xqe2011/saihub/hardware/mechanical/output/preview.png

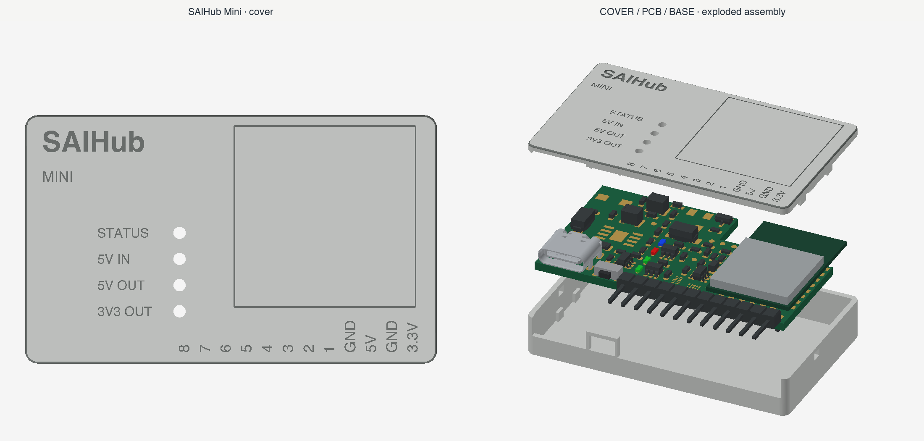
hardware/mechanical/output/preview.png
