xqe2011/saihub/main/src/uart_ctrl.c

/**
 * @name UART control module
 * @file uart_ctrl.c
 * @author xqe2011
 */
#include "uart_ctrl.h"

#include "config.h"
#include "gpio_ctrl.h"
#include "lock.h"
#include "tool.h"

#include <driver/uart.h>
#include <esp_log.h>
#include <freertos/FreeRTOS.h>
#include <freertos/semphr.h>
#include <stdio.h>
#include <string.h>

static const char* tag = "SAIHub-Uart";

static const int uartIdToNum[] = CONFIG_UART_ID_TO_NUM;

typedef struct {
  UartCtrl_Config cfg;
  bool driverInstalled;
  char owner[32];
} UartCtrl_Runtime;

static UartCtrl_Runtime uarts[TOOL_GET_ARRAY_LENGTH(uartIdToNum)];
static SemaphoreHandle_t mutex;

bool UartCtrl_IsValidId(int id)
{
  return id >= 0 && id < (int)TOOL_GET_ARRAY_LENGTH(uartIdToNum);
}

int UartCtrl_GetCount(void)
{
  return (int)TOOL_GET_ARRAY_LENGTH(uartIdToNum);
}

const char* UartCtrl_ParityToString(UartCtrl_Parity p)
{
  switch (p) {
    case UART_CTRL_PARITY_EVEN:
      return "even";
    case UART_CTRL_PARITY_ODD:
      return "odd";
    case UART_CTRL_PARITY_NONE:
    default:
      return "none";
  }
}

bool UartCtrl_ParityFromString(const char* s, UartCtrl_Parity* out)
{
  if (s == NULL || out == NULL) return false;
  if (strcmp(s, "none") == 0) {
    *out = UART_CTRL_PARITY_NONE;
    return true;
  }
  if (strcmp(s, "even") == 0) {
    *out = UART_CTRL_PARITY_EVEN;
    return true;
  }
  if (strcmp(s, "odd") == 0) {
    *out = UART_CTRL_PARITY_ODD;
    return true;
  }
  return false;
}

const char* UartCtrl_EncodingToString(UartCtrl_Encoding e)
{
  return e == UART_CTRL_ENCODING_BYTE ? "byte" : "utf8";
}

bool UartCtrl_EncodingFromString(const char* s, UartCtrl_Encoding* out)
{
  if (s == NULL || out == NULL) return false;
  if (strcmp(s, "utf8") == 0) {
    *out = UART_CTRL_ENCODING_UTF8;
    return true;
  }
  if (strcmp(s, "byte") == 0) {
    *out = UART_CTRL_ENCODING_BYTE;
    return true;
  }
  return false;
}

static uart_port_t UartCtrl_HwPort(int id)
{
  return (uart_port_t)uartIdToNum[id];
}

static uart_word_length_t UartCtrl_ToWordLength(int dataBits)
{
  switch (dataBits) {
    case 5:
      return UART_DATA_5_BITS;
    case 6:
      return UART_DATA_6_BITS;
    case 7:
      return UART_DATA_7_BITS;
    case 8:
    default:
      return UART_DATA_8_BITS;
  }
}

static uart_parity_t UartCtrl_ToParity(UartCtrl_Parity p)
{
  switch (p) {
    case UART_CTRL_PARITY_EVEN:
      return UART_PARITY_EVEN;
    case UART_CTRL_PARITY_ODD:
      return UART_PARITY_ODD;
    case UART_CTRL_PARITY_NONE:
    default:
      return UART_PARITY_DISABLE;
  }
}

static uart_stop_bits_t UartCtrl_ToStopBits(int stopBits)
{
  return stopBits == 2 ? UART_STOP_BITS_2 : UART_STOP_BITS_1;
}

static void UartCtrl_MakeOwner(int id, char* out, size_t outLen)
{
  snprintf(out, outLen, "uart:%d", id);
}

static esp_err_t UartCtrl_ValidateConfig(const UartCtrl_Config* cfg, char* reason, size_t reasonLen)
{
  if (cfg == NULL) return ESP_ERR_INVALID_ARG;
  if (cfg->baudRate < 1) {
    snprintf(reason, reasonLen, "baudRate must be a positive integer.");
    return ESP_ERR_INVALID_ARG;
  }
  if (cfg->dataBits < 5 || cfg->dataBits > 8) {
    snprintf(reason, reasonLen, "dataBits must be 5, 6, 7, or 8.");
    return ESP_ERR_INVALID_ARG;
  }
  if (cfg->stopBits != 1 && cfg->stopBits != 2) {
    snprintf(reason, reasonLen, "stopBits must be 1 or 2.");
    return ESP_ERR_INVALID_ARG;
  }
  if (cfg->rxPin >= 0 && !GpioCtrl_IsValidLogicalPin(cfg->rxPin)) {
    snprintf(reason, reasonLen, "pins.rx is invalid. Use a pin from 0 to %d or omit it.",
             GpioCtrl_GetLogicalCount() - 1);
    return ESP_ERR_INVALID_ARG;
  }
  if (cfg->txPin >= 0 && !GpioCtrl_IsValidLogicalPin(cfg->txPin)) {
    snprintf(reason, reasonLen, "pins.tx is invalid. Use a pin from 0 to %d or omit it.",
             GpioCtrl_GetLogicalCount() - 1);
    return ESP_ERR_INVALID_ARG;
  }
  if (cfg->rxPin >= 0 && cfg->txPin >= 0 && cfg->rxPin == cfg->txPin) {
    snprintf(reason, reasonLen, "pins.rx and pins.tx must be different when both are set.");
    return ESP_ERR_INVALID_ARG;
  }
  if (cfg->enable && cfg->rxPin < 0 && cfg->txPin < 0) {
    snprintf(reason, reasonLen, "enable true requires at least one of pins.rx or pins.tx.");
    return ESP_ERR_INVALID_ARG;
  }
  return ESP_OK;
}

static void UartCtrl_BuildPinResources(const UartCtrl_Config* cfg, Lock_Resource* out, size_t* countOut)
{
  size_t n = 0;
  if (cfg->rxPin >= 0) {
    out[n].kind = LOCK_KIND_GPIO;
    out[n].pin = cfg->rxPin;
    out[n].methods = LOCK_METHOD_READ | LOCK_METHOD_WRITE;
    n++;
  }
  if (cfg->txPin >= 0) {
    out[n].kind = LOCK_KIND_GPIO;
    out[n].pin = cfg->txPin;
    out[n].methods = LOCK_METHOD_READ | LOCK_METHOD_WRITE;
    n++;
  }
  *countOut = n;
}

static void UartCtrl_DisablePinModes(const UartCtrl_Config* cfg)
{
  if (cfg->rxPin >= 0) {
    GpioCtrl_SetConfig(cfg->rxPin, GPIO_CTRL_MODE_DISABLE, false, false, false);
  }
  if (cfg->txPin >= 0) {
    GpioCtrl_SetConfig(cfg->txPin, GPIO_CTRL_MODE_DISABLE, false, false, false);
  }
}

static esp_err_t UartCtrl_StartDriver(int id, const UartCtrl_Config* cfg, char* reason, size_t reasonLen)
{
  Lock_Resource resources[2];
  size_t resourceCount = 0;
  UartCtrl_BuildPinResources(cfg, resources, &resourceCount);

  char owner[32];
  UartCtrl_MakeOwner(id, owner, sizeof(owner));
  Lock_Conflict conflict;
  memset(&conflict, 0, sizeof(conflict));
  esp_err_t aret = Lock_AcquirePeripheral(owner, resources, resourceCount, &conflict);
  if (aret == ESP_ERR_INVALID_STATE) {
    if (conflict.isPeripheral) {
      const char* label = conflict.peripheralLabel[0] ? conflict.peripheralLabel : "a peripheral";
      snprintf(reason, reasonLen, "Pin %d is reserved by %s. Disable %s or use other pins.", conflict.pin, label,
               label);
    } else {
      snprintf(reason, reasonLen,
               "Pin %d is already held by a lock. DELETE that lock or wait until it expires before enabling UART.",
               conflict.pin);
    }
    return ESP_ERR_INVALID_STATE;
  }
  if (aret != ESP_OK) {
    snprintf(reason, reasonLen, "internal");
    return aret;
  }

  UartCtrl_DisablePinModes(cfg);

  uart_config_t ucfg = {
      .baud_rate = cfg->baudRate,
      .data_bits = UartCtrl_ToWordLength(cfg->dataBits),
      .parity = UartCtrl_ToParity(cfg->parity),
      .stop_bits = UartCtrl_ToStopBits(cfg->stopBits),
      .flow_ctrl = UART_HW_FLOWCTRL_DISABLE,
      .source_clk = UART_SCLK_DEFAULT,
  };

  uart_port_t port = UartCtrl_HwPort(id);
  esp_err_t err = uart_driver_install(port, CONFIG_UART_RX_BUF_BYTES, CONFIG_UART_RX_BUF_BYTES, 0, NULL, 0);
  if (err != ESP_OK) {
    Lock_ReleasePeripheral(owner);
    snprintf(reason, reasonLen, "UART resources are unavailable. Disable another UART or try again.");
    return err;
  }
  err = uart_param_config(port, &ucfg);
  if (err != ESP_OK) {
    uart_driver_delete(port);
    Lock_ReleasePeripheral(owner);
    snprintf(reason, reasonLen, "UART configuration was rejected. Check baudRate, dataBits, parity, and stopBits.");
    return err;
  }

  int txHw = cfg->txPin >= 0 ? GpioCtrl_GetHwPin(cfg->txPin) : UART_PIN_NO_CHANGE;
  int rxHw = cfg->rxPin >= 0 ? GpioCtrl_GetHwPin(cfg->rxPin) : UART_PIN_NO_CHANGE;
  /* uart_set_pin(tx, rx, rts, cts) — unused directions use UART_PIN_NO_CHANGE. */
  if (cfg->txPin < 0) txHw = UART_PIN_NO_CHANGE;
  if (cfg->rxPin < 0) rxHw = UART_PIN_NO_CHANGE;
  err = uart_set_pin(port, txHw, rxHw, UART_PIN_NO_CHANGE, UART_PIN_NO_CHANGE);
  if (err != ESP_OK) {
    uart_driver_delete(port);
    Lock_ReleasePeripheral(owner);
    snprintf(reason, reasonLen, "Could not bind UART pins. Use other pins or disable UART.");
    return err;
  }

  UartCtrl_Runtime* u = &uarts[id];
  u->cfg = *cfg;
  u->cfg.enable = true;
  u->driverInstalled = true;
  snprintf(u->owner, sizeof(u->owner), "%s", owner);
  return ESP_OK;
}

esp_err_t UartCtrl_Init(void)
{
  memset(uarts, 0, sizeof(uarts));
  for (size_t i = 0; i < TOOL_GET_ARRAY_LENGTH(uarts); i++) {
    uarts[i].cfg.enable = false;
    uarts[i].cfg.baudRate = 115200;
    uarts[i].cfg.dataBits = 8;
    uarts[i].cfg.parity = UART_CTRL_PARITY_NONE;
    uarts[i].cfg.stopBits = 1;
    uarts[i].cfg.encoding = UART_CTRL_ENCODING_UTF8;
    uarts[i].cfg.rxPin = -1;
    uarts[i].cfg.txPin = -1;
    uarts[i].driverInstalled = false;
    uarts[i].owner[0] = '\0';
  }
  mutex = xSemaphoreCreateMutex();
  TOOL_CHECK_OR_LOG_RETURN(mutex == NULL, "mutex create failed");
  return ESP_OK;
}

esp_err_t UartCtrl_GetConfig(int id, UartCtrl_Config* out)
{
  if (!UartCtrl_IsValidId(id) || out == NULL) return ESP_ERR_INVALID_ARG;
  xSemaphoreTake(mutex, portMAX_DELAY);
  *out = uarts[id].cfg;
  xSemaphoreGive(mutex);
  return ESP_OK;
}

esp_err_t UartCtrl_SetConfig(int id, const UartCtrl_Config* cfg, char* reason, size_t reasonLen)
{
  if (!UartCtrl_IsValidId(id) || cfg == NULL) return ESP_ERR_INVALID_ARG;
  if (UartCtrl_ValidateConfig(cfg, reason, reasonLen) != ESP_OK) return ESP_ERR_INVALID_ARG;

  xSemaphoreTake(mutex, portMAX_DELAY);
  UartCtrl_Runtime* u = &uarts[id];
  UartCtrl_Config previous = u->cfg;
  bool wasInstalled = u->driverInstalled;
  char previousOwner[32];
  snprintf(previousOwner, sizeof(previousOwner), "%s", u->owner);

  if (!cfg->enable) {
    if (u->driverInstalled) {
      uart_driver_delete(UartCtrl_HwPort(id));
      u->driverInstalled = false;
    }
    if (u->owner[0] != '\0') {
      Lock_ReleasePeripheral(u->owner);
      u->owner[0] = '\0';
    }
    UartCtrl_DisablePinModes(&u->cfg);
    u->cfg = *cfg;
    u->cfg.enable = false;
    xSemaphoreGive(mutex);
    return ESP_OK;
  }

  /* Enabling or reconfiguring while enabled: stop current driver first, then start with new pins. */
  if (u->driverInstalled) {
    uart_driver_delete(UartCtrl_HwPort(id));
    u->driverInstalled = false;
  }
  if (u->owner[0] != '\0') {
    Lock_ReleasePeripheral(u->owner);
    u->owner[0] = '\0';
  }
  UartCtrl_DisablePinModes(&u->cfg);

  esp_err_t err = UartCtrl_StartDriver(id, cfg, reason, reasonLen);
  if (err != ESP_OK) {
    /* Best-effort restore of previous enabled state. */
    if (wasInstalled && previous.enable) {
      char restoreReason[160];
      if (UartCtrl_StartDriver(id, &previous, restoreReason, sizeof(restoreReason)) != ESP_OK) {
        ESP_LOGW(tag, "Failed to restore UART %d after config error: %s", id, restoreReason);
        u->cfg = previous;
        u->cfg.enable = false;
        (void)previousOwner;
      }
    } else {
      u->cfg = *cfg;
      u->cfg.enable = false;
    }
    xSemaphoreGive(mutex);
    return err;
  }
  xSemaphoreGive(mutex);
  return ESP_OK;
}

esp_err_t UartCtrl_Transmit(int id, const uint8_t* data, size_t len, char* reason, size_t reasonLen)
{
  if (!UartCtrl_IsValidId(id)) return ESP_ERR_INVALID_ARG;
  if (data == NULL && len > 0) return ESP_ERR_INVALID_ARG;
  if (len > CONFIG_UART_MAX_PAYLOAD_BYTES) {
    snprintf(reason, reasonLen, "data is too large. Send at most %u bytes per request.",
             (unsigned)CONFIG_UART_MAX_PAYLOAD_BYTES);
    return ESP_ERR_INVALID_SIZE;
  }

  xSemaphoreTake(mutex, portMAX_DELAY);
  UartCtrl_Runtime* u = &uarts[id];
  if (!u->cfg.enable || !u->driverInstalled) {
    snprintf(reason, reasonLen, "UART %d is not enabled. POST /uart/%d/config with enable true first.", id, id);
    xSemaphoreGive(mutex);
    return ESP_ERR_INVALID_STATE;
  }
  if (u->cfg.txPin < 0) {
    snprintf(reason, reasonLen, "UART %d has no tx pin. POST /uart/%d/config with pins.tx set.", id, id);
    xSemaphoreGive(mutex);
    return ESP_ERR_INVALID_STATE;
  }
  if (len == 0) {
    xSemaphoreGive(mutex);
    return ESP_OK;
  }
  int written = uart_write_bytes(UartCtrl_HwPort(id), data, len);
  xSemaphoreGive(mutex);
  if (written < 0 || (size_t)written != len) {
    snprintf(reason, reasonLen, "internal");
    return ESP_FAIL;
  }
  return ESP_OK;
}

esp_err_t UartCtrl_Receive(int id, uint8_t* out, size_t maxLen, size_t* outLen, char* reason, size_t reasonLen)
{
  if (!UartCtrl_IsValidId(id) || out == NULL || outLen == NULL) return ESP_ERR_INVALID_ARG;
  *outLen = 0;

  xSemaphoreTake(mutex, portMAX_DELAY);
  UartCtrl_Runtime* u = &uarts[id];
  if (!u->cfg.enable || !u->driverInstalled) {
    snprintf(reason, reasonLen, "UART %d is not enabled. POST /uart/%d/config with enable true first.", id, id);
    xSemaphoreGive(mutex);
    return ESP_ERR_INVALID_STATE;
  }
  if (u->cfg.rxPin < 0) {
    snprintf(reason, reasonLen, "UART %d has no rx pin. POST /uart/%d/config with pins.rx set.", id, id);
    xSemaphoreGive(mutex);
    return ESP_ERR_INVALID_STATE;
  }
  size_t want = maxLen;
  if (want > CONFIG_UART_MAX_PAYLOAD_BYTES) want = CONFIG_UART_MAX_PAYLOAD_BYTES;
  int n = uart_read_bytes(UartCtrl_HwPort(id), out, want, 0);
  xSemaphoreGive(mutex);
  if (n < 0) {
    snprintf(reason, reasonLen, "internal");
    return ESP_FAIL;
  }
  *outLen = (size_t)n;
  return ESP_OK;
}

esp_err_t UartCtrl_Flush(int id, char* reason, size_t reasonLen)
{
  if (!UartCtrl_IsValidId(id)) return ESP_ERR_INVALID_ARG;

  xSemaphoreTake(mutex, portMAX_DELAY);
  UartCtrl_Runtime* u = &uarts[id];
  if (!u->cfg.enable || !u->driverInstalled) {
    snprintf(reason, reasonLen, "UART %d is not enabled. POST /uart/%d/config with enable true first.", id, id);
    xSemaphoreGive(mutex);
    return ESP_ERR_INVALID_STATE;
  }
  esp_err_t err = uart_flush_input(UartCtrl_HwPort(id));
  xSemaphoreGive(mutex);
  if (err != ESP_OK) {
    snprintf(reason, reasonLen, "internal");
    return err;
  }
  return ESP_OK;
}
