xqe2011/saihub/main/include/tool_call.h

/**
 * @name Shared tool invoke (MCP + Lua)
 * @file tool_call.h
 * @author xqe2011
 */
#ifndef TOOL_CALL_H__
#define TOOL_CALL_H__

#include "gpio_ctrl.h"

#include <cJSON.h>
#include <stdbool.h>
#include <stddef.h>

typedef struct {
  bool ok;
  cJSON* payload; /* caller-owned on success; NULL on error */
  char reason[256];
  int httpStatus; /* REST status to use if this failure is uncaught by a script */
} ToolCall_Result;

/**
 * Invoke a pin/power/lock tool by MCP name.
 * Does not handle run_script. Caller owns payload and must cJSON_Delete it.
 * Empty-success tools return payload {"ok":true}.
 * via is logged as the call source (mcp|lua).
 */
ToolCall_Result ToolCall_Invoke(const char* via, const char* name, cJSON* args);

/** Capture trace events without constructing a JSON response. Caller frees events on success. */
ToolCall_Result ToolCall_TraceCapture(cJSON* args, GpioCtrl_TraceEvent** eventsOut, size_t* eventCountOut);

#endif
